zibontaroka/SafeSwitch-IoT/photos/Inter pin form.JPG

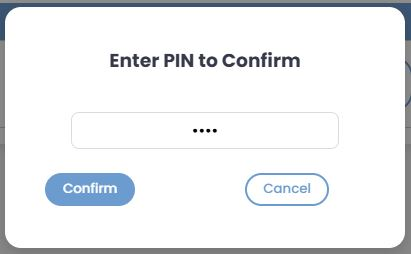
photos/Inter pin form.JPG
