zibontaroka/SafeSwitch-IoT/photos/lineman-handover table.JPG

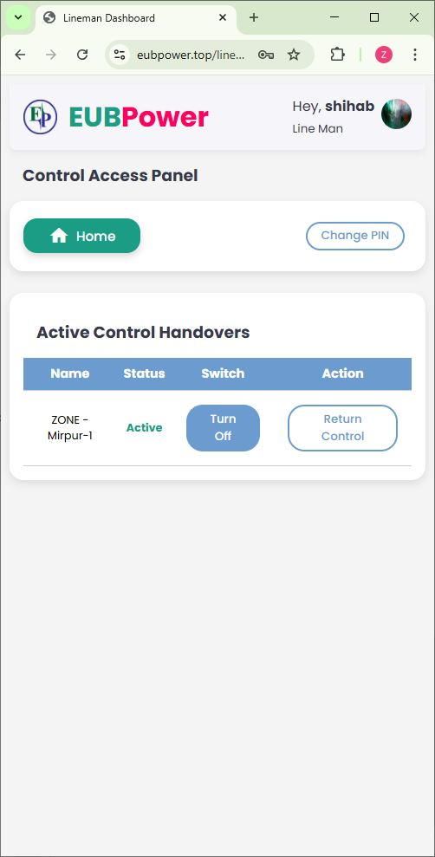
photos/lineman-handover table.JPG
