zibontaroka/SafeSwitch-IoT/photos/login page.JPG

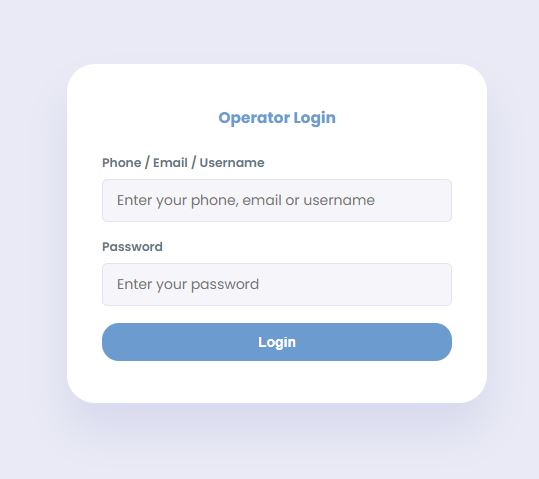
photos/login page.JPG
