zibontaroka/SafeSwitch-IoT/photos/oparator-desable zone.JPG

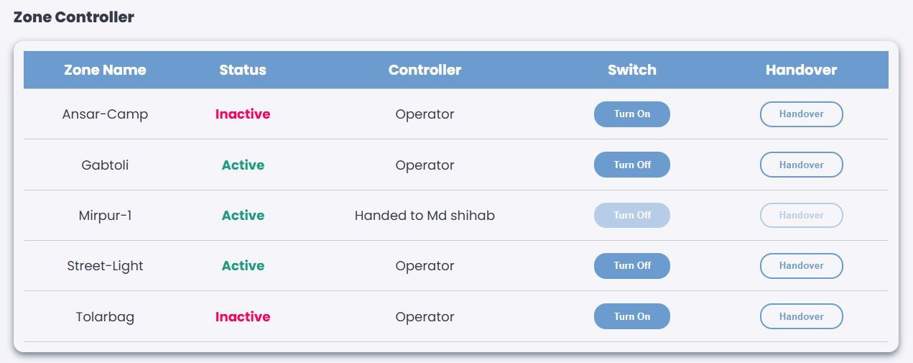
photos/oparator-desable zone.JPG
