zibontaroka/SafeSwitch-IoT/photos/PCB_back.jpg

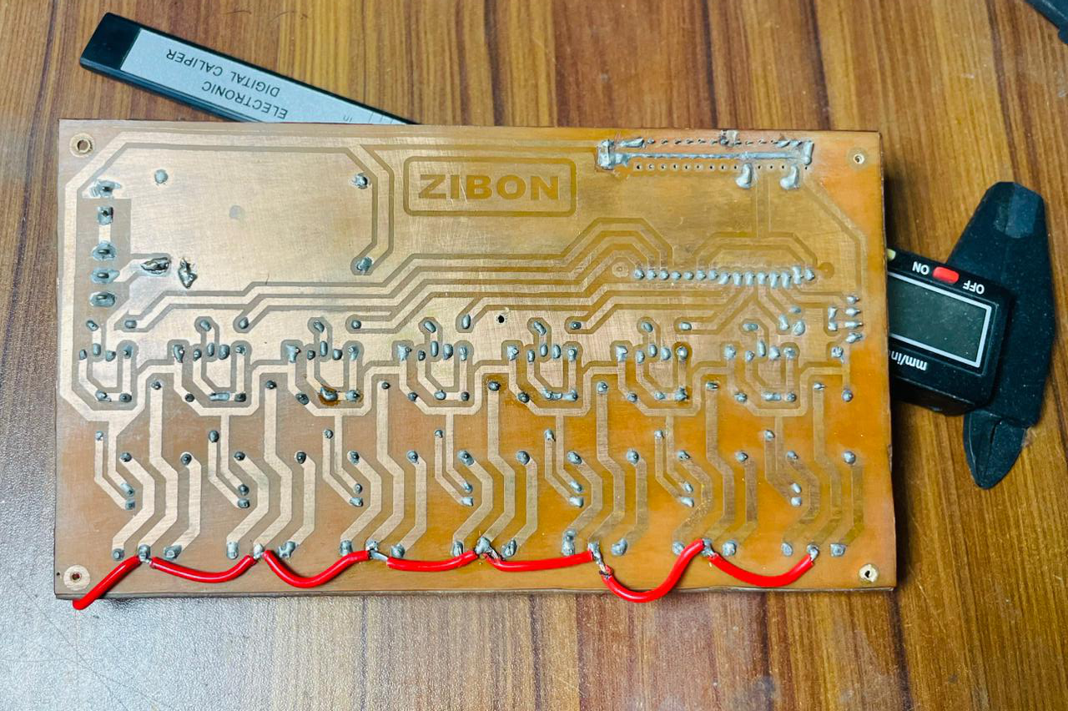
photos/PCB_back.jpg
