zibontaroka/SafeSwitch-IoT/photos/Zone controll.JPG

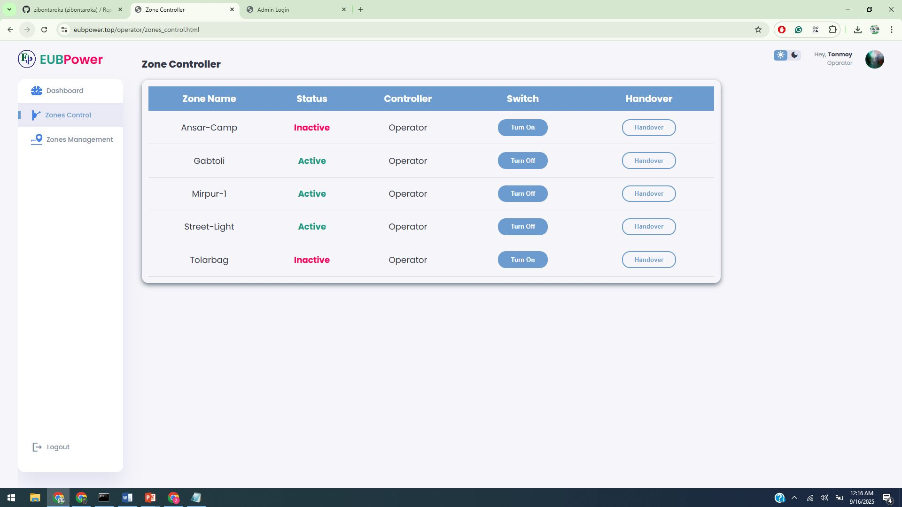
photos/Zone controll.JPG
