zibontaroka/SafeSwitch-IoT/photos/PCB_font.jpg

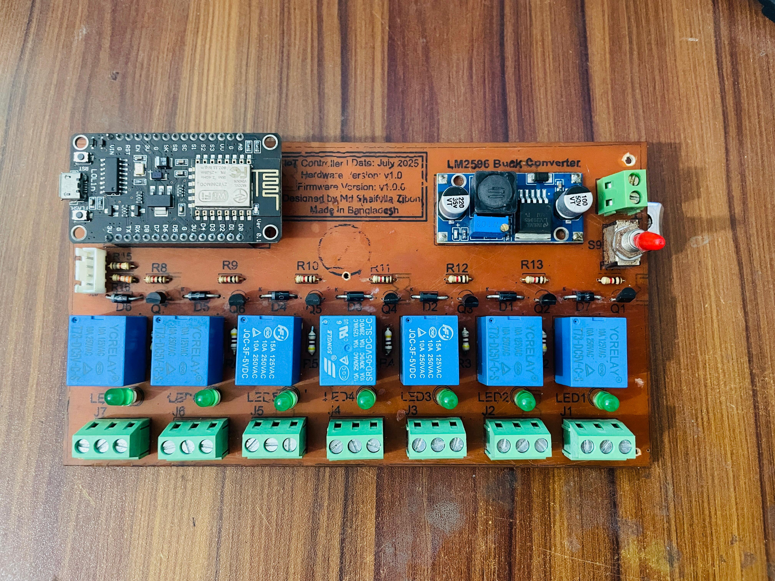
photos/PCB_font.jpg
